ChristianIannella/ICSP/Media/IMG_3568.JPG

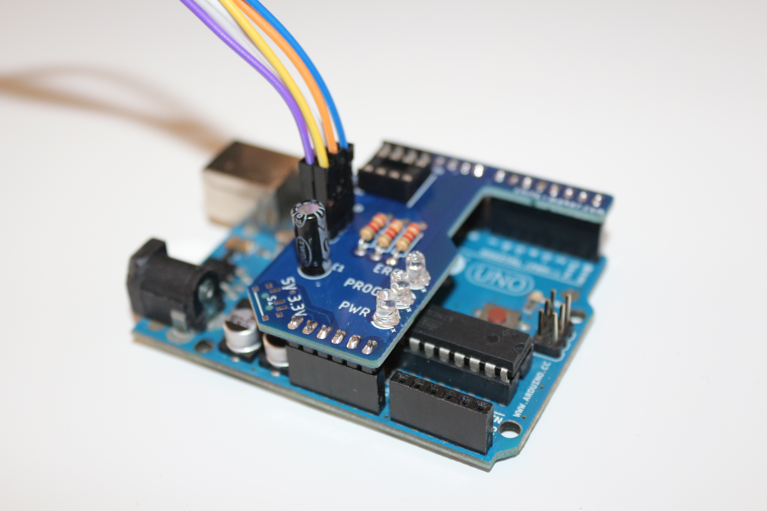
Media/IMG_3568.JPG
