ChristianIannella/ICSP/Media/IMG_3588.JPG

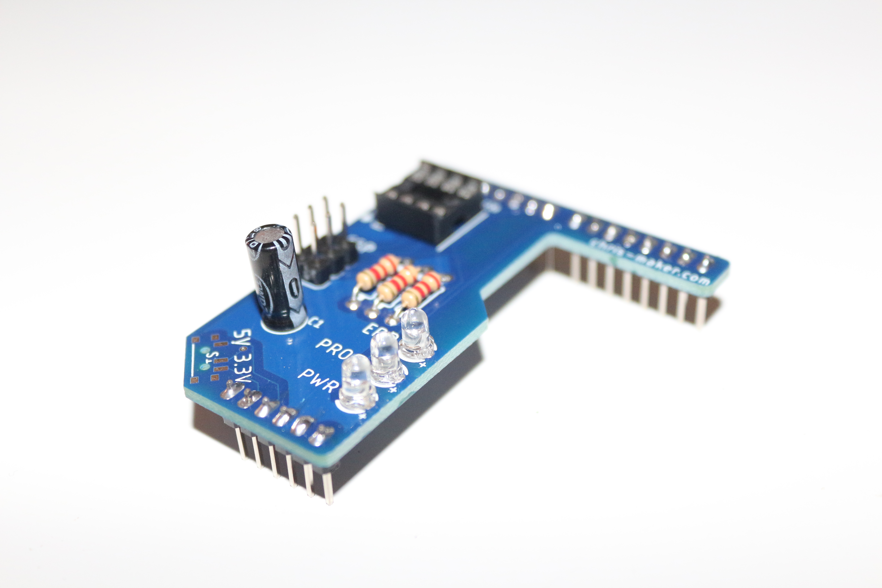
Media/IMG_3588.JPG
